nasim-raj-laskar/EdgeBlink/pcb/dct.kicad_sch

## KiCad design pcb/dct.kicad_sch (2025-08-14)

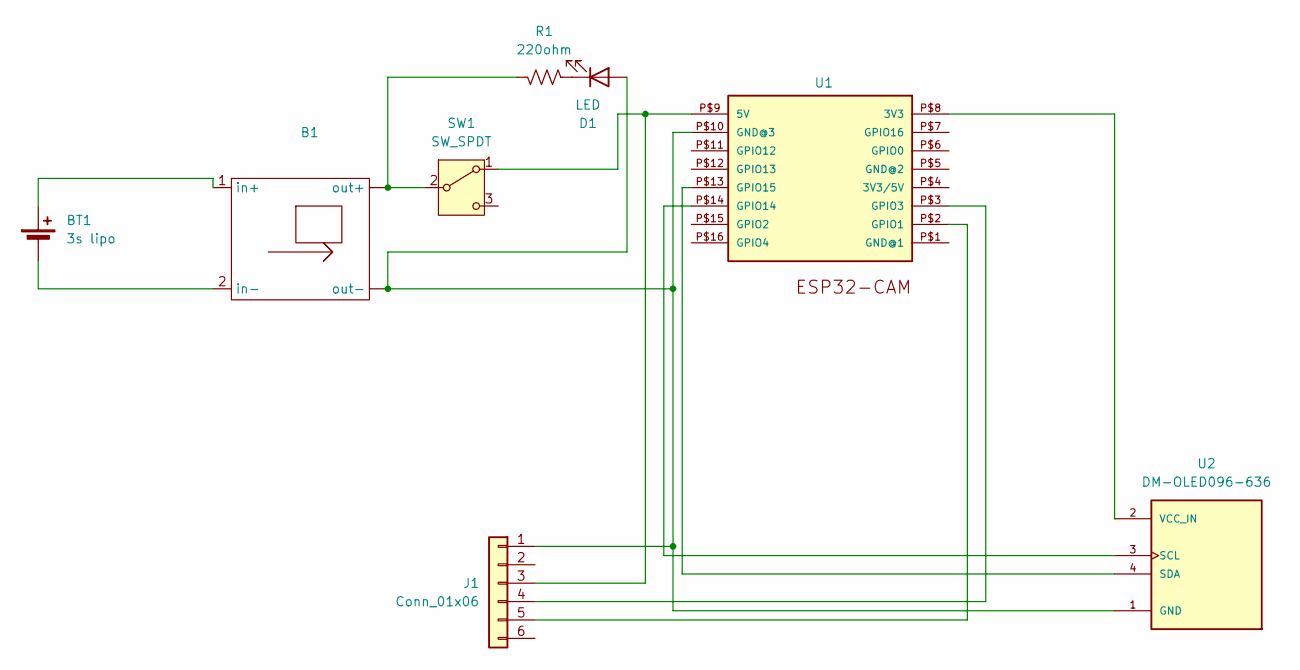
[picture p7: schematic dct.kicad_sch]

Parts:
B1: PinHeader_2x02_P2.54mm_Vertical
BT1: 3s lipo; AMASS_XT30U-F_1x02_P5.0mm_Vertical
D1: LED; LED_D5.0mm
J1: Conn_01x06; PinHeader_1x06_P2.54mm_Vertical
R1: 220ohm; R_Axial_DIN0204_L3.6mm_D1.6mm_P7.62mm_Horizontal
SW1: SW_SPDT; SW_SPDT_CK_JS102011SAQN
U1: ESP32-CAM
U2: DM-OLED096-636; MODULE_DM-OLED096-636; PARTREV 2018-09-10

Connections:
unnamed: B1.1 (in+), BT1.1 (+)
unnamed: B1.2 (in-), BT1.2 (-)
unnamed: B1. (out+), D1.2 (A), J1.1, R1.2, SW1.2 (B), U1.P$10 (GND@3), U2.1 (GND)
unnamed: D1.1 (K), R1.1
unnamed: J1.3, SW1.1 (A), U1.P$9 (5V)
unnamed: J1.4, U1.P$3 (GPIO3)
unnamed: J1.5, U1.P$2 (GPIO1)
unnamed: U1.P$8 (3V3), U2.2 (VCC_IN)
unnamed: U1.P$13 (GPIO15), U2.4 (SDA)
unnamed: U1.P$14 (GPIO14), U2.3 (SCL)
